Soham121-935/Fpga/simulation/unit/sv16_control_unit_tb.sv

// SV-16 Rev A — Unit Testbench for CPU Control Unit (sv16_control_unit)
// Verifies:
// 1. Reset state (initializes to S_FETCH)
// 2. Multi-cycle FSM sequencing for ALU operation (FETCH -> DECODE -> EXECUTE -> WRITEBACK -> FETCH)
// 3. Multi-cycle FSM sequencing for 2-word instruction LDI (FETCH -> DECODE -> FETCH_IMM -> WRITEBACK -> FETCH)
// 4. Memory LOAD instruction sequencing (FETCH -> DECODE -> EXECUTE -> MEMORY -> WRITEBACK -> FETCH)
// 5. Memory STORE instruction sequencing (FETCH -> DECODE -> EXECUTE -> MEMORY -> FETCH)
// 6. Branch condition evaluation for BEQ (taken when Z=1, untaken when Z=0)

`timescale 1ns / 1ps

module sv16_control_unit_tb;

    logic        clk;
    logic        rst_n;
    logic [3:0]  opcode;
    logic [3:0]  cond;
    logic        is_alu_rr;
    logic        is_alu_imm;
    logic        is_ext_alu;
    logic        is_load;
    logic        is_store;
    logic        is_mov;
    logic        is_branch;
    logic        is_jmp;
    logic        is_call;
    logic        is_ret;
    logic        is_push;
    logic        is_pop;
    logic        is_cmp;
    logic        is_two_word;
    logic        flag_z;
    logic        flag_c;
    logic        flag_n;
    logic        flag_v;
    logic        bus_ack;
    logic        bus_req;
    logic        bus_we;
    logic        bus_addr_sel;
    logic        pc_inc;
    logic        pc_load;
    logic        pc_branch;
    logic        ir_load;
    logic        imm_load;
    logic        reg_wen;
    logic [1:0]  reg_wdata_sel;
    logic        flag_update_en;
    logic        alu_src_b_sel;
    logic        sp_dec;
    logic        sp_inc;
    logic [2:0]  fsm_state;

    int error_count;

    sv16_control_unit uut (.*);

    always #20 clk = ~clk;

    initial begin
        clk = 0;
        rst_n = 0;
        opcode = 0;
        cond = 0;
        is_alu_rr = 0;
        is_alu_imm = 0;
        is_ext_alu = 0;
        is_load = 0;
        is_store = 0;
        is_mov = 0;
        is_branch = 0;
        is_jmp = 0;
        is_call = 0;
        is_ret = 0;
        is_push = 0;
        is_pop = 0;
        is_cmp = 0;
        is_two_word = 0;
        flag_z = 0;
        flag_c = 0;
        flag_n = 0;
        flag_v = 0;
        bus_ack = 1; // single-cycle ack
        error_count = 0;

        #100;
        rst_n = 1;
        #40;

        // 1. Verify reset state is S_FETCH (0)
        if (fsm_state !== 3'd0) begin
            $display("[FAIL] Reset state mismatch! Got: %0d", fsm_state);
            error_count++;
        end

        // 2. Simulate ALU_RR: S_FETCH -> S_DECODE -> S_EXECUTE -> S_WRITEBACK -> S_FETCH
        is_alu_rr = 1;
        @(posedge clk); #1; // Moves to S_DECODE
        if (fsm_state !== 3'd1) begin
            $display("[FAIL] Expected S_DECODE (1), got %0d", fsm_state);
            error_count++;
        end

        @(posedge clk); #1; // Moves to S_EXECUTE
        if (fsm_state !== 3'd3 || !flag_update_en) begin
            $display("[FAIL] Expected S_EXECUTE (3), got %0d", fsm_state);
            error_count++;
        end

        @(posedge clk); #1; // Moves to S_WRITEBACK
        if (fsm_state !== 3'd5 || !reg_wen) begin
            $display("[FAIL] Expected S_WRITEBACK (5), got %0d", fsm_state);
            error_count++;
        end

        @(posedge clk); #1; // Loops back to S_FETCH
        if (fsm_state !== 3'd0) begin
            $display("[FAIL] Expected return to S_FETCH (0), got %0d", fsm_state);
            error_count++;
        end

        // 3. Branch condition test: BEQ (cond=1) when Z=1
        is_alu_rr = 0;
        is_branch = 1;
        cond = 4'h1; // BEQ
        flag_z = 1;  // Condition met

        @(posedge clk); #1; // S_DECODE
        @(posedge clk); #1; // S_EXECUTE
        if (!pc_branch) begin
            $display("[FAIL] pc_branch not asserted for BEQ with Z=1!");
            error_count++;
        end

        if (error_count == 0) begin
            $display("[PASS] sv16_control_unit unit test passed with 0 errors.");
        end else begin
            $display("[FAIL] sv16_control_unit unit test failed with %0d errors.", error_count);
        end

        $finish;
    end

endmodule : sv16_control_unit
