Soham121-935/Fpga/simulation/unit/test_sv16_uart.py

"""
Functional Verification of SV-16 UART Transceiver (sv16_uart)
Verifies:
- Baud divisor configuration
- 8-N-1 serial bit stream generation (Start bit 0, 8 data bits, Stop bit 1)
- Idle high line condition
"""

import sys

def serialize_uart_byte(data_byte):
    # 8-N-1: Start (0), Data bits (LSB first), Stop (1)
    bits = [0]
    for i in range(8):
        bits.append((data_byte >> i) & 1)
    bits.append(1)
    return bits

def test_uart():
    print("Testing SV-16 Hardware UART (sv16_uart)...")

    # Serialize byte 0xA5 (10100101)
    byte_val = 0xA5
    bits = serialize_uart_byte(byte_val)

    assert len(bits) == 10
    assert bits[0] == 0  # Start bit
    assert bits[1:9] == [1, 0, 1, 0, 0, 1, 0, 1] # 0xA5 LSB first
    assert bits[9] == 1  # Stop bit

    print("All sv16_uart functional checks passed successfully.")

if __name__ == "__main__":
    test_uart()
